zuzivian/eecs327-pan-tilt-camera/Atmel/example_uart/src/ov2640_table_registers.c

/**
 * \file
 *
 * \brief Register table for OV2640 CMOS image sensor.
 *
 * Copyright (c) 2014-2015 Atmel Corporation. All rights reserved.
 *
 * \asf_license_start
 *
 * \page License
 *
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
 * 3. The name of Atmel may not be used to endorse or promote products derived
 *    from this software without specific prior written permission.
 *
 * 4. This software may only be redistributed and used in connection with an
 *    Atmel microcontroller product.
 *
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
 * \asf_license_stop
 *
 */
/*
 * Support and FAQ: visit <a href="http://www.atmel.com/design-support/">Atmel Support</a>
 */

#include "board.h"
#include <ov2640.h>

#ifdef __cplusplus
extern "C" {
#endif

/**
 * \defgroup OV2640_CMOS_image_sensor_registers_group
 *
 * This file defines several arrays. Each of them contain adress of OV2640
 * register and corresponding value for a specific configuration.
 * There are seven different configuration:
 *       -  OV2640_QVGA_YUV422_10FPS[]
 *       -  OV2640_QVGA_YUV422_15FPS[]
 *       -  OV2640_QVGA_YUV422_20FPS[]
 *       -  OV2640_QVGA_YUV422_30FPS[]
 *       -  OV2640_QVGA_RGB888[]
 *       -  OV2640_QQVGA_YUV422[]
 *       -  OV2640_QQVGA_RGB888[]
 *       -  OV2640_TEST_PATTERN[]
 *       -  OV2640_VGA_YUV422_20FPS[]
 * These values have been obtained from OV2640 datasheet and OmniVision Developer Kit.
 * @{
 */

/**
 * My configuration
 */
const ov_reg OV2640_JPEG_INIT[] = {
	{0xff, 0x00},
	{0x2c, 0xff},
	{0x2e, 0xdf},
	{0xff, 0x01},
	{0x3c, 0x32},
	{0x11, 0x01},	//{0x11, 0x03}, //{0x11, 0x04},	//
	{0x09, 0x02},
	{0x04, 0x28},
	{0x13, 0xe5},
	{0x14, 0x48},
	{0x2c, 0x0c},
	{0x33, 0x78},
	{0x3a, 0x33},
	{0x3b, 0xfB},
	{0x3e, 0x00},
	{0x43, 0x11},
	{0x16, 0x10},
	{0x39, 0x92},
	{0x35, 0xda},
	{0x22, 0x1a},
	{0x37, 0xc3},
	{0x23, 0x00},
	{0x34, 0xc0},
	{0x36, 0x1a},
	{0x06, 0x88},
	{0x07, 0xc0},
	{0x0d, 0x87},
	{0x0e, 0x41},
	{0x4c, 0x00},
	{0x48, 0x00},
	{0x5B, 0x00},
	{0x42, 0x03},
	{0x4a, 0x81},
	{0x21, 0x99},
	{0x24, 0x40},
	{0x25, 0x38},
	{0x26, 0x82},
	{0x5c, 0x00},
	{0x63, 0x00},
	{0x61, 0x70},
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
	
	{0x12, 0x40},
	{0xd3, 0x04},	//{0xd3, 0x7f},
	{0xc0, 0x16},
	{0xC1, 0x12},
	{0x8c, 0x00},
	{0x86, 0x3d},
	{0x50, 0x00},
	{0x51, 0x2C},
	{0x52, 0x24},
	{0x53, 0x00},
	{0x54, 0x00},
	{0x55, 0x00},
	{0x5A, 0x2c},
	{0x5b, 0x24},
	{0x5c, 0x00},
	{0xFF, 0xFF}
};

const ov_reg OV2640_YUV422[] = {
	{0xFF, 0x00},
	{0x05, 0x00},
	{0xDA, 0x10},
	{0xD7, 0x03},
	{0xDF, 0x00},
	{0x33, 0x80},
	{0x3C, 0x40},
	{0xe1, 0x77},
	{0x00, 0x00},
	{0xFF, 0xFF}
};

const ov_reg OV2640_JPEG[] = {
	{0xe0, 0x14},
	{0xe1, 0x77},
	{0xe5, 0x1f},
	{0xd7, 0x03},
	{0xda, 0x10},
	{0xe0, 0x00},
	{0xFF, 0x01},
	{0x04, 0x08},
	{0xFF, 0xFF}
};

const ov_reg OV2640_JPEG_320x240[] = {
	{0xff, 0x01},
	{0x12, 0x40},
	{0x17, 0x11},
	{0x18, 0x43},
	{0x19, 0x00},
	{0x1a, 0x4b},
	{0x32, 0x09},
	{0x4f, 0xca},
	{0x50, 0xa8},
	{0x5a, 0x23},
	{0x6d, 0x00},
	{0x39, 0x12},
	{0x35, 0xda},
	{0x22, 0x1a},
	{0x37, 0xc3},
	{0x23, 0x00},
	{0x34, 0xc0},
	{0x36, 0x1a},
	{0x06, 0x88},
	{0x07, 0xc0},
	{0x0d, 0x87},
	{0x0e, 0x41},
	{0x4c, 0x00},
	{0xff, 0x00},
	{0xe0, 0x04},
	{0xc0, 0x64},
	{0xc1, 0x4b},
	{0x86, 0x35},
	{0x50, 0x89},
	{0x51, 0xc8},
	{0x52, 0x96},
	{0x53, 0x00},
	{0x54, 0x00},
	{0x55, 0x00},
	{0x57, 0x00},
	{0x5a, 0x50},
	{0x5b, 0x3c},
	{0x5c, 0x00},
	{0xe0, 0x00},
	{0xFF, 0xFF}
};

/* JPG 640x480 */
const ov_reg OV2640_JPEG_640x480[]  =
{
	{0xff, 0x01},
	{0x11, 0x01},
	{0x12, 0x00}, // Bit[6:4]: Resolution selection//0x02???
	{0x17, 0x11}, // HREFST[10:3]
	{0x18, 0x75}, // HREFEND[10:3]
	{0x32, 0x36}, // Bit[5:3]: HREFEND[2:0]; Bit[2:0]: HREFST[2:0]
	{0x19, 0x01}, // VSTRT[9:2]
	{0x1a, 0x97}, // VEND[9:2]
	{0x03, 0x0f}, // Bit[3:2]: VEND[1:0]; Bit[1:0]: VSTRT[1:0]
	{0x37, 0x40},
	{0x4f, 0xbb},
	{0x50, 0x9c},
	{0x5a, 0x57},
	{0x6d, 0x80},
	{0x3d, 0x34},
	{0x39, 0x02},
	{0x35, 0x88},
	{0x22, 0x0a},
	{0x37, 0x40},
	{0x34, 0xa0},
	{0x06, 0x02},
	{0x0d, 0xb7},
	{0x0e, 0x01},
	
	{0xff, 0x00},
	{0xe0, 0x04},
	{0xc0, 0xc8},
	{0xc1, 0x96},
	{0x86, 0x3d},
	{0x50, 0x89},
	{0x51, 0x90},
	{0x52, 0x2c},
	{0x53, 0x00},
	{0x54, 0x00},
	{0x55, 0x88},
	{0x57, 0x00},
	{0x5a, 0xa0},
	{0x5b, 0x78},
	{0x5c, 0x00},
	{0xd3, 0x04},
	{0xe0, 0x00},
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
	{0x5c, 0x88},
	{0x5d, 0x60},

	{0xac, 0x6e},
	{0xbe, 0xff},
	{0xbf, 0x00},

	/* 320x240 */

	{0x31, 0x50},
	{0x32, 0x78},
	{0x82, 0x3f},

	/* YUV */
	{0x12, 0x00},
	{0x36, 0x3f},
	{0x53, 0x00},

	{0x33, 0xc4},
	{0x1b, 0x89},
	{0x22, 0x03},

	/* VSYNC, inverse */
	{0x28, 0x2},

	{0xFF, 0xFF}
};

/**
 * \brief Addresses and values of the OV2640 registers for the
 * OV2640_QVGA_YUV422_15FPS configuration:
 *  - 320*240 pixel by picture (QVGA)
 *  - pixel data in YUV422 format (Y1, U, Y2, V)
 *  - 15 frames per second
 */
const ov_reg OV2640_QVGA_YUV422_15FPS[] = {
	{0x0e, 0x00},

	{0x12, 0x80},
	/* flag for soft reset delay */
	{0xFE, 0x05},
	{0x13, 0x00},

	/**************************************************************/
	/*  30fps  11 01 ;clock_divider ;sysclk=24MHz at XCLK=24MHz   */
	/*  20fps  11 02 ;clock_divider ;sysclk=16MHz at XCLK=24MHz   */
	/*  15fps  11 03 ;clock_divider ;sysclk=12MHz at XCLK=24MHz   */
	/*  10fps  11 05 ;sysclk=8MHz at XCLK=24MHz                   */
	/*  7p5fps 11 07 ;sysclk=6MHz at XCLK=24MHz                   */
	/**************************************************************/
	{0x11, 0x03},
	/**************************************************************/

	{0x12, 0x00},
	{0xd5, 0x10},
	{0x0c, (OV2640_REG0C_MIRROR_ENABLE | OV2640_REG0C_FLIP_ENABLE | OV2640_REG0C_MAX_EXPOSURE(2) | OV2640_REG0C_YUV_SWAP_ENABLE)},
	{0x0d, 0x34},
	{0x16, 0x01},
	{0x17, 0x25},
	{0x18, 0xa0},
	{0x19, 0x03},
	{0x1a, 0xf0},
	{0x1b, 0x89},
	{0x22, 0x03},
	{0x29, 0x18},
	{0x2b, 0xf8},
	{0x2c, 0x01},
	{0x31, 0xa0},
	{0x32, 0xf0},
	{0x33, 0xc4},
	{0x3a, 0xb4},
	{0x36, 0x3f},

	{0x04, 0x60},
	{0x27, 0x80},
	{0x3d, 0x0f},
	{0x3e, 0x80},
	{0x3f, 0x40},
	{0x40, 0x7f},
	{0x41, 0x6a},
	{0x42, 0x29},
	{0x44, 0xe5},
	{0x45, 0x41},
	{0x47, 0x02},
	{0x49, 0x64},
	{0x4a, 0xa1},
	{0x4b, 0x70},
	{0x4c, 0x1a},
	{0x4d, 0x50},
	{0x4e, 0x13},
	{0x64, 0x00},
	{0x67, 0x88},
	{0x68, 0x1a},

	{0x14, 0x38},
	{0x24, 0x3c},
	{0x25, 0x30},
	{0x26, 0x72},
	{0x50, 0x97},
	{0x51, 0x7e},
	{0x52, 0x00},
	{0x53, 0x00},
	{0x20, 0x00},
	{0x21, 0x23},
	/*********************************/
	/* To enable Static Test Pattern */
	/*********************************/
	/* {0x38, 0x07}, */
	/* {0x84, 0x02}, */

	/*********************************/
	/* Normal Mode / No test pattern */
	{0x38, 0x14},
	/*********************************/
	{0xe9, 0x00},
	{0x56, 0x55},
	{0x57, 0xff},
	{0x58, 0xff},
	{0x59, 0xff},
	{0x5f, 0x04},
	{0xec, 0x00},
	{0x13, 0xff},

	{0x80, 0x7f},
	{0x81, 0x3f},
	{0x82, 0x32},
	{0x83, 0x01},
	{0x38, 0x11},
	{0x85, 0x00},
	{0x86, 0x03},
	{0x87, 0x01},
	{0x88, 0x05},
	{0x89, 0x30},
	{0x8d, 0x30},
	{0x8f, 0x85},
	{0x93, 0x30},
	{0x95, 0x85},
	{0x99, 0x30},
	{0x9b, 0x85},

	{0x9c, 0x08},
	{0x9d, 0x12},
	{0x9e, 0x23},
	{0x9f, 0x45},
	{0xa0, 0x55},
	{0xa1, 0x64},
	{0xa2, 0x72},
	{0xa3, 0x7f},
	{0xa4, 0x8b},
	{0xa5, 0x95},
	{0xa6, 0xa7},
	{0xa7, 0xb5},
	{0xa8, 0xcb},
	{0xa9, 0xdd},
	{0xaa, 0xec},
	{0xab, 0x1a},

	{0xce, 0x78},
	{0xcf, 0x6e},
	{0xd0, 0x0a},
	{0xd1, 0x0c},
	{0xd2, 0x84},
	{0xd3, 0x90},
	{0xd4, 0x1e},

	{0x5a, 0x24},
	{0x5b, 0x1f},
	{0x5c, 0x88},
	{0x5d, 0x60},

	{0xac, 0x6e},
	{0xbe, 0xff},
	{0xbf, 0x00},

	/* 320x240 */

	{0x31, 0x50},
	{0x32, 0x78},
	{0x82, 0x3f},

	/* YUV */
	{0x12, 0x00},
	{0x36, 0x3f},
	{0x53, 0x00},

	{0x33, 0xc4},
	{0x1b, 0x89},
	{0x22, 0x03},

	/* VSYNC, inverse */
	{0x28, 0x2},

	{0xFF, 0xFF}
};

/**
 * \brief Addresses and values of the OV2640 registers for the
 * OV2640_QVGA_YUV422_20FPS configuration:
 *  - 320*240 pixel by picture (QVGA)
 *  - pixel data in YUV422 format (Y1, U, Y2, V)
 *  - 20 frames per second
 */
const ov_reg OV2640_QVGA_YUV422_20FPS[] = {
	{0x0e, 0x00},

	{0x12, 0x80},
	/* flag for soft reset delay */
	{0xFE, 0x05},
	{0x13, 0x00},

	/**************************************************************/
	/*  30fps  11 01 ;clock_divider ;sysclk=24MHz at XCLK=24MHz   */
	/*  20fps  11 02 ;clock_divider ;sysclk=16MHz at XCLK=24MHz   */
	/*  15fps  11 03 ;clock_divider ;sysclk=12MHz at XCLK=24MHz   */
	/*  10fps  11 05 ;sysclk=8MHz at XCLK=24MHz                   */
	/*  7p5fps 11 07 ;sysclk=6MHz at XCLK=24MHz                   */
	/**************************************************************/
	{0x11, 0x02},
	/**************************************************************/

	{0x12, 0x00},
	{0xd5, 0x10},
	{0x0c, (OV2640_REG0C_MIRROR_ENABLE | OV2640_REG0C_FLIP_ENABLE | OV2640_REG0C_MAX_EXPOSURE(2) | OV2640_REG0C_YUV_SWAP_ENABLE)},
	{0x0d, 0x34},
	{0x16, 0x01},
	{0x17, 0x25},
	{0x18, 0xa0},
	{0x19, 0x03},
	{0x1a, 0xf0},
	{0x1b, 0x89},
	{0x22, 0x03},
	{0x29, 0x18},
	{0x2b, 0xf8},
	{0x2c, 0x01},
	{0x31, 0xa0},
	{0x32, 0xf0},
	{0x33, 0xc4},
	{0x3a, 0xb4},
	{0x36, 0x3f},

	{0x04, 0x60},
	{0x27, 0x80},
	{0x3d, 0x0f},
	{0x3e, 0x80},
	{0x3f, 0x40},
	{0x40, 0x7f},
	{0x41, 0x6a},
	{0x42, 0x29},
	{0x44, 0xe5},
	{0x45, 0x41},
	{0x47, 0x02},
	{0x49, 0x64},
	{0x4a, 0xa1},
	{0x4b, 0x70},
	{0x4c, 0x1a},
	{0x4d, 0x50},
	{0x4e, 0x13},
	{0x64, 0x00},
	{0x67, 0x88},
	{0x68, 0x1a},

	{0x14, 0x38},
	{0x24, 0x3c},
	{0x25, 0x30},
	{0x26, 0x72},
	{0x50, 0x97},
	{0x51, 0x7e},
	{0x52, 0x00},
	{0x53, 0x00},
	{0x20, 0x00},
	{0x21, 0x23},
	/*********************************/
	/* To enable Static Test Pattern */
	/*********************************/
	/* {0x38, 0x07}, */
	/* {0x84, 0x02}, */

	/*********************************/
	/* Normal Mode / No test pattern */
	{0x38, 0x14},
	/*********************************/
	{0xe9, 0x00},
	{0x56, 0x55},
	{0x57, 0xff},
	{0x58, 0xff},
	{0x59, 0xff},
	{0x5f, 0x04},
	{0xec, 0x00},
	{0x13, 0xff},

	{0x80, 0x7f},
	{0x81, 0x3f},
	{0x82, 0x32},
	{0x83, 0x01},
	{0x38, 0x11},
	{0x85, 0x00},
	{0x86, 0x03},
	{0x87, 0x01},
	{0x88, 0x05},
	{0x89, 0x30},
	{0x8d, 0x30},
	{0x8f, 0x85},
	{0x93, 0x30},
	{0x95, 0x85},
	{0x99, 0x30},
	{0x9b, 0x85},

	{0x9c, 0x08},
	{0x9d, 0x12},
	{0x9e, 0x23},
	{0x9f, 0x45},
	{0xa0, 0x55},
	{0xa1, 0x64},
	{0xa2, 0x72},
	{0xa3, 0x7f},
	{0xa4, 0x8b},
	{0xa5, 0x95},
	{0xa6, 0xa7},
	{0xa7, 0xb5},
	{0xa8, 0xcb},
	{0xa9, 0xdd},
	{0xaa, 0xec},
	{0xab, 0x1a},

	{0xce, 0x78},
	{0xcf, 0x6e},
	{0xd0, 0x0a},
	{0xd1, 0x0c},
	{0xd2, 0x84},
	{0xd3, 0x90},
	{0xd4, 0x1e},

	{0x5a, 0x24},
	{0x5b, 0x1f},
	{0x5c, 0x88},
	{0x5d, 0x60},

	{0xac, 0x6e},
	{0xbe, 0xff},
	{0xbf, 0x00},

	/* 320x240 */

	{0x31, 0x50},
	{0x32, 0x78},
	{0x82, 0x3f},

	/* YUV */
	{0x12, 0x00},
	{0x36, 0x3f},
	{0x53, 0x00},

	{0x33, 0xc4},
	{0x1b, 0x89},
	{0x22, 0x03},

	/* VSYNC, inverse */
	{0x28, 0x2},

	{0xFF, 0xFF}
};

/**
 * \brief Addresses and values of the OV2640 registers for the
 * OV2640_QVGA_YUV422_30FPS configuration:
 *  - 320*240 pixel by picture (QVGA)
 *  - pixel data in YUV422 format (Y1, U, Y2, V)
 *  - 30 frames per second
 */
const ov_reg OV2640_QVGA_YUV422_30FPS[] = {
	{0x0e, 0x00},

	{0x12, 0x80},
	/* flag for soft reset delay */
	{0xFE, 0x05},
	{0x13, 0x00},

	/**************************************************************/
	/*  30fps  11 01 ;clock_divider ;sysclk=24MHz at XCLK=24MHz   */
	/*  20fps  11 02 ;clock_divider ;sysclk=16MHz at XCLK=24MHz   */
	/*  15fps  11 03 ;clock_divider ;sysclk=12MHz at XCLK=24MHz   */
	/*  10fps  11 05 ;sysclk=8MHz at XCLK=24MHz                   */
	/*  7p5fps 11 07 ;sysclk=6MHz at XCLK=24MHz                   */
	/**************************************************************/
	{0x11, 0x01},
	/**************************************************************/

	{0x12, 0x00},
	{0xd5, 0x10},
	{0x0c, (OV2640_REG0C_MIRROR_ENABLE | OV2640_REG0C_FLIP_ENABLE | OV2640_REG0C_MAX_EXPOSURE(2) | OV2640_REG0C_YUV_SWAP_ENABLE)},
	{0x0d, 0x34},
	{0x16, 0x01},
	{0x17, 0x25},
	{0x18, 0xa0},
	{0x19, 0x03},
	{0x1a, 0xf0},
	{0x1b, 0x89},
	{0x22, 0x03},
	{0x29, 0x18},
	{0x2b, 0xf8},
	{0x2c, 0x01},
	{0x31, 0xa0},
	{0x32, 0xf0},
	{0x33, 0xc4},
	{0x3a, 0xb4},
	{0x36, 0x3f},

	{0x04, 0x60},
	{0x27, 0x80},
	{0x3d, 0x0f},
	{0x3e, 0x80},
	{0x3f, 0x40},
	{0x40, 0x7f},
	{0x41, 0x6a},
	{0x42, 0x29},
	{0x44, 0xe5},
	{0x45, 0x41},
	{0x47, 0x02},
	{0x49, 0x64},
	{0x4a, 0xa1},
	{0x4b, 0x70},
	{0x4c, 0x1a},
	{0x4d, 0x50},
	{0x4e, 0x13},
	{0x64, 0x00},
	{0x67, 0x88},
	{0x68, 0x1a},

	{0x14, 0x38},
	{0x24, 0x3c},
	{0x25, 0x30},
	{0x26, 0x72},
	{0x50, 0x97},
	{0x51, 0x7e},
	{0x52, 0x00},
	{0x53, 0x00},
	{0x20, 0x00},
	{0x21, 0x23},
	/*********************************/
	/* To enable Static Test Pattern */
	/*********************************/
	/* {0x38, 0x07}, */
	/* {0x84, 0x02}, */

	/*********************************/
	/* Normal Mode / No test pattern */
	{0x38, 0x14},
	/*********************************/
	{0xe9, 0x00},
	{0x56, 0x55},
	{0x57, 0xff},
	{0x58, 0xff},
	{0x59, 0xff},
	{0x5f, 0x04},
	{0xec, 0x00},
	{0x13, 0xff},

	{0x80, 0x7f},
	{0x81, 0x3f},
	{0x82, 0x32},
	{0x83, 0x01},
	{0x38, 0x11},
	{0x85, 0x00},
	{0x86, 0x03},
	{0x87, 0x01},
	{0x88, 0x05},
	{0x89, 0x30},
	{0x8d, 0x30},
	{0x8f, 0x85},
	{0x93, 0x30},
	{0x95, 0x85},
	{0x99, 0x30},
	{0x9b, 0x85},

	{0x9c, 0x08},
	{0x9d, 0x12},
	{0x9e, 0x23},
	{0x9f, 0x45},
	{0xa0, 0x55},
	{0xa1, 0x64},
	{0xa2, 0x72},
	{0xa3, 0x7f},
	{0xa4, 0x8b},
	{0xa5, 0x95},
	{0xa6, 0xa7},
	{0xa7, 0xb5},
	{0xa8, 0xcb},
	{0xa9, 0xdd},
	{0xaa, 0xec},
	{0xab, 0x1a},

	{0xce, 0x78},
	{0xcf, 0x6e},
	{0xd0, 0x0a},
	{0xd1, 0x0c},
	{0xd2, 0x84},
	{0xd3, 0x90},
	{0xd4, 0x1e},

	{0x5a, 0x24},
	{0x5b, 0x1f},
	{0x5c, 0x88},
	{0x5d, 0x60},

	{0xac, 0x6e},
	{0xbe, 0xff},
	{0xbf, 0x00},

	/* 320x240 */

	{0x31, 0x50},
	{0x32, 0x78},
	{0x82, 0x3f},

	/* YUV */
	{0x12, 0x00},
	{0x36, 0x3f},
	{0x53, 0x00},

	{0x33, 0xc4},
	{0x1b, 0x89},
	{0x22, 0x03},

	/* VSYNC, inverse */
	{0x28, 0x2},

	{0xFF, 0xFF}
};

/**
 * \brief Addresses and values of the OV2640 registers for the
 * OV2640_QVGA_RGB888 configuration:
 *  - 320*240 pixel by picture (QVGA)
 *  - pixel data in RGB format (8-8-8)
 */
const ov_reg OV2640_QVGA_RGB888[] = {
	{0x0e, 0x00},

	{0x12, 0x80},
	{0x13, 0x00},

	{0x11, 0x01},
	{0x12, 0x00},
	{0xd5, 0x10},
	{0x0c, 0x12},
	{0x0d, 0x34},
	{0x17, 0x25},
	{0x18, 0xa0},
	{0x19, 0x03},
	{0x1a, 0xf0},
	{0x1b, 0x89},
	{0x22, 0x03},
	{0x29, 0x18},
	{0x2b, 0xf8},
	{0x2c, 0x01},
	{0x31, 0xa0},
	{0x32, 0xf0},
	{0x33, 0xc4},
	{0x3a, 0xb4},
	{0x36, 0x3f},

	{0x04, 0x60},
	{0x27, 0x80},
	{0x3d, 0x0f},
	{0x3e, 0x80},
	{0x3f, 0x40},
	{0x40, 0x7f},
	{0x41, 0x6a},
	{0x42, 0x29},
	{0x44, 0xe5},
	{0x45, 0x41},
	{0x47, 0x02},
	{0x49, 0x64},
	{0x4a, 0xa1},
	{0x4b, 0x70},
	{0x4c, 0x1a},
	{0x4d, 0x50},
	{0x4e, 0x13},
	{0x64, 0x00},
	{0x67, 0x88},
	{0x68, 0x1a},

	{0x14, 0x38},
	{0x24, 0x3c},
	{0x25, 0x30},
	{0x26, 0x72},
	{0x50, 0x97},
	{0x51, 0x7e},
	{0x52, 0x00},
	{0x53, 0x00},
	{0x20, 0x00},
	{0x21, 0x23},
	{0x38, 0x14},
	{0xe9, 0x00},
	{0x56, 0x55},
	{0x57, 0xff},
	{0x58, 0xff},
	{0x59, 0xff},
	{0x5f, 0x04},
	{0xec, 0x00},
	{0x13, 0xff},

	{0x80, 0x7f},
	{0x81, 0x3f},
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
	{0xbe, 0xff},
	{0xbf, 0x00},

	/* 640x480 */

	{0x31, 0xA0},
	{0x32, 0xF0},
	{0x82, 0x3f},

	/* YUV */
	{0x12, 0x00},
	{0x36, 0x3f},
	{0x53, 0x00},

	{0x33, 0xc4},
	{0x1b, 0x89},
	{0x22, 0x03},

	/* VSYNC, inverse */
	{0x28, 0x2},

	{0xFF, 0xFF}
};

/* @} */

#ifdef __cplusplus
}
#endif
