zuzivian/eecs327-pan-tilt-camera/Atmel/example_uart/src/camera.h

/*
 * camera.h
 *
 * Created: 2/22/2019 12:48:57 AM
 *  Author: Yifei
 */ 

#ifndef CAMERA_H_
#define CAMERA_H_

#include <asf.h>
#include "timer_interface.h"

#define TWI_CLK     (400000UL);
#define IM_BUF_LEN	60000

volatile uint8_t image_buff[IM_BUF_LEN];
static volatile uint32_t g_ul_vsync_flag; 
volatile  uint32_t start_idx;





/** HSYNC pin */
#define PIN_OV_HSYNC                   { PIO_PA16, PIOA, ID_PIOA, \
	PIO_INPUT, PIO_PULLUP | \
PIO_IT_RISE_EDGE }

/** VSYNC pin */
#define PIN_OV_VSYNC                   { PIO_PA15, PIOA, ID_PIOA, \
	PIO_INPUT, PIO_PULLUP | \
PIO_IT_RISE_EDGE }

/** OV_HSYNC pin definition */
#define OV_HSYNC_GPIO                  PIO_PA16_IDX
#define OV_HSYNC_FLAGS                 (PIO_PULLUP | PIO_IT_RISE_EDGE)
#define OV_HSYNC_MASK                  PIO_PA16
#define OV_HSYNC_PIO                   PIOA
#define OV_HSYNC_ID                    ID_PIOA
#define OV_HSYNC_TYPE                  PIO_PULLUP

/** OV_VSYNC pin definition */
#define OV_VSYNC_GPIO                  PIO_PA15_IDX
#define OV_VSYNC_FLAGS                 (PIO_PULLUP | PIO_IT_RISE_EDGE)
#define OV_VSYNC_MASK                  PIO_PA15
#define OV_VSYNC_PIO                   PIOA
#define OV_VSYNC_ID                    ID_PIOA
#define OV_VSYNC_TYPE                  PIO_PULLUP

/** PCK0 */
#define PIN_PCK1                       (PIO_PA17_IDX)
#define PIN_PCK1_FLAGS                 (PIO_PERIPH_B | PIO_DEFAULT)

/******************************* TWI definition
 *********************************/
/** TWI0 data pin */
#define PIN_TWI_TWD0                   {PIO_PA3A_TWD0, PIOA, ID_PIOA, \
                                         PIO_PERIPH_A, PIO_DEFAULT}

/** TWI0 clock pin */
#define PIN_TWI_TWCK0                  {PIO_PA4A_TWCK0, PIOA, ID_PIOA,	\
                                         PIO_PERIPH_A, PIO_DEFAULT}

/** TWI0 Data pins definition */
#define TWI0_DATA_GPIO                 PIO_PA3_IDX
#define TWI0_DATA_FLAGS                (PIO_PERIPH_A | PIO_DEFAULT)
#define TWI0_DATA_MASK                 PIO_PA3
#define TWI0_DATA_PIO                  PIOA
#define TWI0_DATA_ID                   ID_PIOA
#define TWI0_DATA_TYPE                 PIO_PERIPH_A
#define TWI0_DATA_ATTR                 PIO_DEFAULT

/** TWI0 clock pins definition */
#define TWI0_CLK_GPIO                  PIO_PA4_IDX
#define TWI0_CLK_FLAGS                 (PIO_PERIPH_A | PIO_DEFAULT)
#define TWI0_CLK_MASK                  PIO_PA4
#define TWI0_CLK_PIO                   PIOA
#define TWI0_CLK_ID                    ID_PIOA
#define TWI0_CLK_TYPE                  PIO_PERIPH_A
#define TWI0_CLK_ATTR                  PIO_DEFAULT

/** TWI0 pins */
#define PINS_TWI0                      PIN_TWI_TWD0, PIN_TWI_TWCK0

#define ID_BOARD_TWI		               ID_TWI0
#define BOARD_TWI			                 TWI0
#define BOARD_TWI_IRQn		             TWI0_IRQn

/** OV_SW_OVT pin definition */
#define OV_SW_OVT_GPIO                 PIO_PB6_IDX
#define OV_SW_OVT_FLAGS                (PIO_OUTPUT_1 | PIO_DEFAULT)
#define OV_SW_OVT_MASK                 PIO_PB6
#define OV_SW_OVT_PIO                  PIOB
#define OV_SW_OVT_ID                   ID_PIOB
#define OV_SW_OVT_TYPE                 PIO_OUTPUT_1 

#define OV_DATA_BUS_MASK               (0xFF000000UL)
#define OV_DATA_BUS_PIO                PIOA
#define OV_DATA_BUS_ID                 ID_PIOA
#define OV_DATA_BUS_TYPE               PIO_INPUT
#define OV_DATA_BUS_ATTR               PIO_DEFAULT


#define OV_DATA_BUS_D0                 PIO_PA24_IDX
#define OV_DATA_BUS_D1                 PIO_PA25_IDX
#define OV_DATA_BUS_D2                 PIO_PA26_IDX
#define OV_DATA_BUS_D3                 PIO_PA27_IDX
#define OV_DATA_BUS_D4                 PIO_PA28_IDX
#define OV_DATA_BUS_D5                 PIO_PA29_IDX
#define OV_DATA_BUS_D6                 PIO_PA30_IDX
#define OV_DATA_BUS_D7                 PIO_PA31_IDX

#define OV_DATA_BUS_FLAGS              (PIO_INPUT | PIO_PULLUP)
#define OV_DATA_BUS_MASK               (0xFF000000UL)
#define OV_DATA_BUS_PIO                PIOA
#define OV_DATA_BUS_ID                 ID_PIOA
#define OV_DATA_BUS_TYPE               PIO_INPUT
#define OV_DATA_BUS_ATTR               PIO_DEFAULT

#define OV_RST_GPIO                    PIO_PA20_IDX
#define OV_RST_FLAGS                   (PIO_OUTPUT_1 | PIO_DEFAULT)
#define OV_RST_MASK                    PIO_PA20
#define OV_RST_PIO                     PIOA
#define OV_RST_ID                      ID_PIOA
#define OV_RST_TYPE                    PIO_OUTPUT_1



void vsync_handler(uint32_t ul_id, uint32_t ul_mask);
void init_vsync_interrupts(void);
void pio_capture_init(Pio *p_pio, uint32_t ul_id);
uint8_t pio_capture_to_buffer(Pio *p_pio, uint8_t *uc_buf,
uint32_t ul_size);
void capture_init(void);
uint32_t find_image_len(void);
uint8_t start_capture(void);


#endif /* CAMERA_H_ */
